duck531a98/esp8266-weather-station-epaper/bitmaps/config.bmp

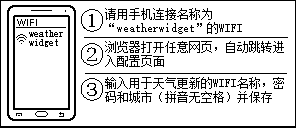
bitmaps/config.bmp
