duck531a98/esp8266-weather-station-epaper/pics/20170623_232157.jpg

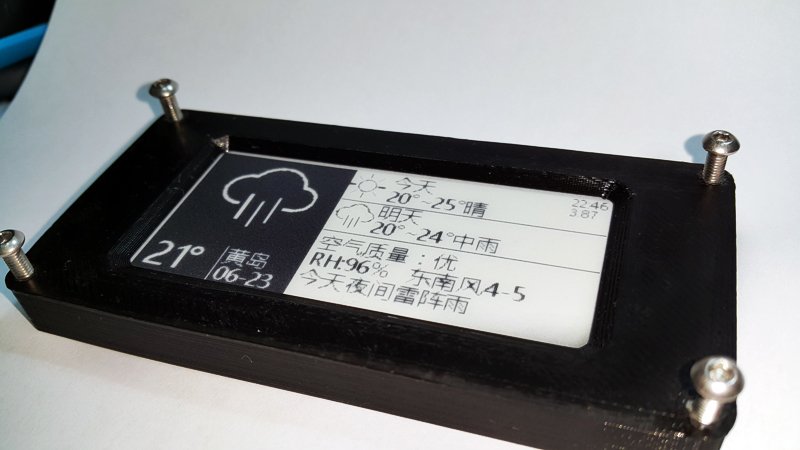
pics/20170623_232157.jpg
