duck531a98/esp8266-weather-station-epaper/pics/20170624_214405.jpg

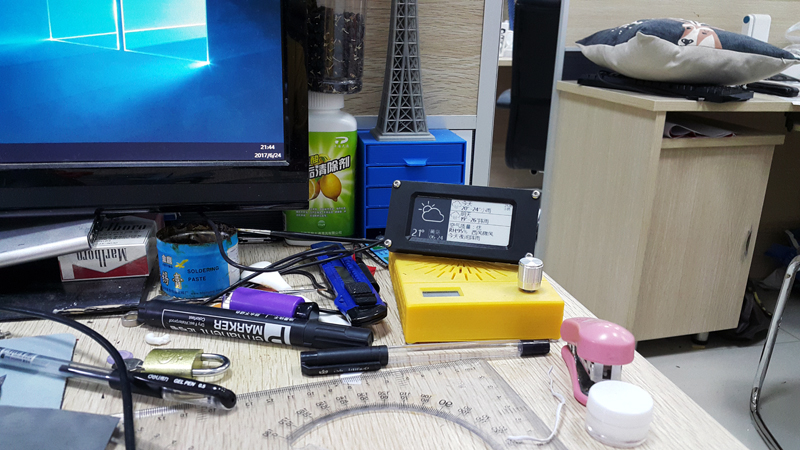
pics/20170624_214405.jpg
