duck531a98/esp8266-weather-station-epaper/pics/20170624_214454.jpg

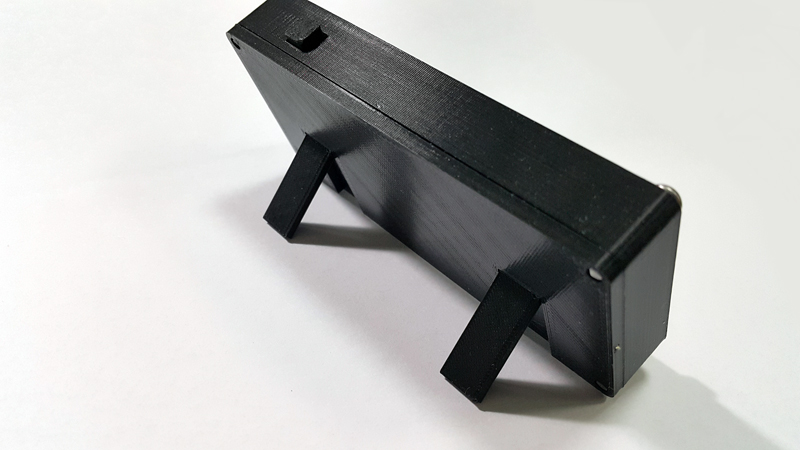
pics/20170624_214454.jpg
