duck531a98/esp8266-weather-station-epaper/pics/20170705_221111.jpg

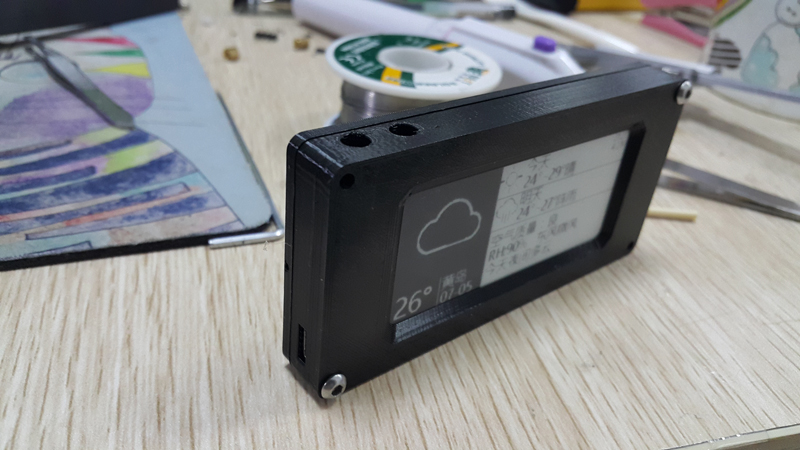
pics/20170705_221111.jpg
