duck531a98/esp8266-weather-station-epaper/pics/20170721_232400.jpg

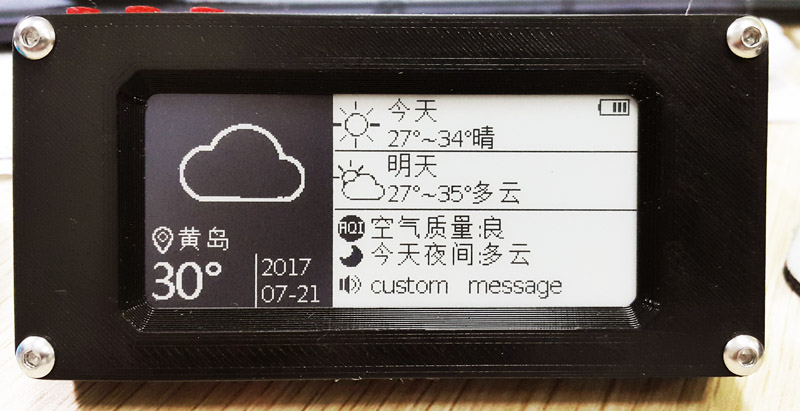
pics/20170721_232400.jpg
