duck531a98/esp8266-weather-station-epaper/pics/20200505_004032.jpg

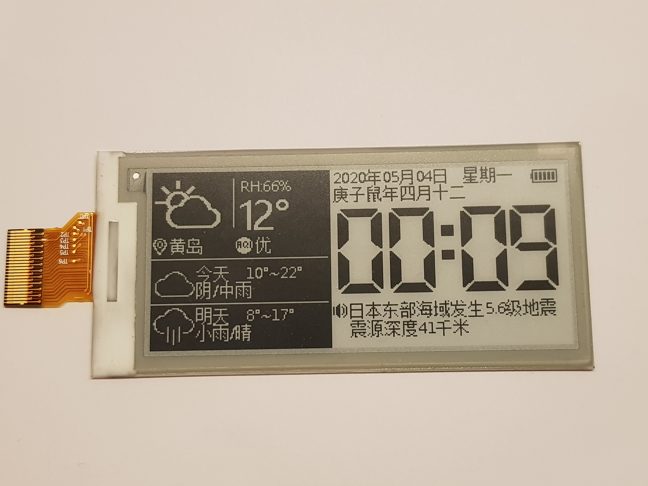
pics/20200505_004032.jpg
