duck531a98/esp8266-weather-station-epaper/EPD_drive.h

#pragma once
 extern unsigned char UNICODEbuffer[200];
 extern const char* fontname;
#ifndef _EPD_DRIVE_H_
#define _EPD_DRIVE_H_
//#include "spline.h"
#include <ESP8266WiFi.h>

  static const unsigned char GDVol[] = {0x03,0x00}; // Gate voltage +15V/-15V
  static  unsigned char GDOControl[]={0x01,39,1,0x00}; //for 1.54inch
  static  unsigned char softstart[]={0x0c,0xd7,0xd6,0x9d};
  static  unsigned char Rambypass[] = {0x21,0x8f};   // Display update
  static unsigned char MAsequency[] = {0x22,0xf0};    // clock 
  static  unsigned char SDVol[] = {0x04,0x0a}; // Source voltage +15V/-15V
  static  unsigned char VCOMVol[] = {0x2c,0xa8}; // VCOM 7c 0xa8
  static unsigned char GateVol[]={0x03,0xea};
  
  static  unsigned char BOOSTERFB[] = {0xf0,0x1f}; // Source voltage +15V/-15V
  static  unsigned char DummyLine[] = {0x3a,0x01}; // 4 dummy line per gate
  static  unsigned char Gatetime[] = {0x3b,B1000};  // 2us per line
  static  unsigned char BorderWavefrom[] = {0x3c,0x63};  // Border
  static  unsigned char RamDataEntryMode[] = {0x11,0x01};  // Ram data entry mode
  static const unsigned char LUTDefault_part[31] = {
    0x32, // command
    0x10,0x18,0x18,0x08,0x18,0x18,0x08,0x00,0x00,0x00,0x00,0x00,0x00,0x00,0x00,0x00,0x00,0x00,0x00,0x00,
    0x13,0x14,0x44,0x12,0x00,0x00,0x00,0x00,0x00,0x00,
    /* 10 wb  01 bw
     * 10 H REPEAT 3
     * 10 H 01 L REPEAT 1
     * 10 H 01 L REPEAT 4
     * 01 L REPEAT 1
     * 10 H 01 L REPEAT 4
     * 10 H 01 L REPEAT 4
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
0x8A ,0x4A ,0x0F ,
0x83 ,0x43 ,0x0C ,
0x06 ,0x4A ,0x04 };
const unsigned char lut_bb_bz03[] ={
  0x24,
0x0E  ,0x14 ,0x01 ,
0x8A ,0x06 ,0x04 ,
0x8A ,0x4A ,0x0F ,
0x83 ,0x43 ,0x0C ,
0x06 ,0x4A ,0x04};
*/
const unsigned char lut_vcomDC_bz03[] ={
0x20,
0x0a ,0x00 ,0x06 ,
0x0a ,0x00 ,0x06 ,
0x0a ,0x00 ,0x06 ,
0x0a ,0x00 ,0x06 ,
0x00 ,0x00 ,0x00 };
const unsigned char lut_ww_bz03[] ={//w
0x21,
0x4a ,0x00 ,0x06,
0x8a ,0x00 ,0x06 ,
0x4A ,0x00 ,0x06 ,
0x8a ,0x00 ,0x06 ,
0x00 ,0x00 ,0x00};
const unsigned char lut_bw_bz03[] ={//b
  0x22,
0x8a  ,0x00 ,0x06 ,
0x4A ,0x00 ,0x06 ,
0x8A ,0x00 ,0x06 ,
0x4a ,0x00 ,0x06 ,
0x00 ,0x00 ,0x00};
const unsigned char lut_wb_bz03[] ={
  0x23,
0x8a  ,0x00 ,0x06 ,
0x4A ,0x00 ,0x06 ,
0x8A ,0x00 ,0x06 ,
0x4a ,0x00 ,0x06 ,
0x00 ,0x00 ,0x00};
const unsigned char lut_bb_bz03[] ={
  0x24,
0x4a ,0x00 ,0x06,
0x8a ,0x00 ,0x06 ,
0x4A ,0x00 ,0x06 ,
0x8a ,0x00 ,0x06 ,
0x00 ,0x00 ,0x00};
const unsigned char lut_vcomDC_part_bz03[] ={
0x20,
0x0a ,0x00 ,0x03 ,
0x00 ,0x00 ,0x00 ,
0x00 ,0x00 ,0x00 ,
0x00 ,0x00 ,0x00 ,
0x00 ,0x00 ,0x00  };
const unsigned char lut_ww_part_bz03[] ={//w
0x21,
0x0a ,0x00 ,0x03,
0x00 ,0x00 ,0x00 ,
0x00 ,0x00 ,0x00 ,
0x00 ,0x00 ,0x00 ,
0x00 ,0x00 ,0x00 };
const unsigned char lut_bb_part_bz03[] ={//01
  0x22,
0x0a ,0x00 ,0x03 ,
0x00 ,0x00 ,0x00 ,
0x00 ,0x00 ,0x00 ,
0x00 ,0x00 ,0x00 ,
0x00 ,0x00 ,0x00 };
const unsigned char lut_bw_part_bz03[] ={//10
  0x23,
0x4a ,0x00 ,0x03 ,
0x00 ,0x00 ,0x00 ,
0x00 ,0x00 ,0x00 ,
0x00 ,0x00 ,0x00 ,
0x00 ,0x00 ,0x00 };
const unsigned char lut_wb_part_bz03[] ={//10
  0x24,
0x8a  ,0x00 ,0x03 ,
0x00 ,0x00 ,0x00 ,
0x00 ,0x00 ,0x00 ,
0x00 ,0x00 ,0x00 ,
0x00 ,0x00 ,0x00};

const unsigned char lut_vcomDC_wf32[] ={
0x20,
0x0a ,0x00 ,0x10 ,
0x0a ,0x00 ,0x10 ,
0x0a ,0x00 ,0x10 ,
0x0a ,0x00 ,0x10 ,
0x00 ,0x00 ,0x00 };
const unsigned char lut_ww_wf32[] ={//ww
0x21,
0x4a ,0x00 ,0x10,
0x8a ,0x00 ,0x10 ,
0x4A ,0x00 ,0x10 ,
0x8A ,0x00 ,0x10 ,
0x00 ,0x00 ,0x00};
const unsigned char lut_bw_wf32[] ={//b
  0x22,
0x8a  ,0x00 ,0x10 ,
0x4A ,0x00 ,0x10 ,
0x8A ,0x00 ,0x10 ,
0x4a ,0x00 ,0x10 ,
0x00 ,0x00 ,0x00};
const unsigned char lut_wb_wf32[] ={//bb
  0x23,
0x8a  ,0x00 ,0x10 ,
0x4A ,0x00 ,0x10 ,
0x8A ,0x00 ,0x10 ,
0x4a ,0x00 ,0x10 ,
0x00 ,0x00 ,0x00};
const unsigned char lut_bb_wf32[] ={//w
  0x24,
0x8a ,0x00 ,0x10,
0x4a ,0x00 ,0x10 ,
0x8A ,0x00 ,0x10 ,
0x8A ,0x00 ,0x10 ,
0x00 ,0x00 ,0x00};
const unsigned char lut_vcomDC_part_wf32[] ={
0x20,
0x0a ,0x00 ,0x04 ,
0x00 ,0x00 ,0x00 ,
0x00 ,0x00 ,0x00 ,
0x00 ,0x00 ,0x00 ,
0x00 ,0x00 ,0x00  };
const unsigned char lut_ww_part_wf32[] ={//w
0x21,
0x0a ,0x00 ,0x04,
0x00 ,0x00 ,0x00 ,
0x00 ,0x00 ,0x00 ,
0x00 ,0x00 ,0x00 ,
0x00 ,0x00 ,0x00 };
const unsigned char lut_bb_part_wf32[] ={//01
0x22,
0x0a ,0x00 ,0x04 ,
0x00 ,0x00 ,0x00 ,
0x00 ,0x00 ,0x00 ,
0x00 ,0x00 ,0x00 ,
0x00 ,0x00 ,0x00 };
const unsigned char lut_bw_part_wf32[] ={//10
0x23,
0x4a ,0x00 ,0x12 ,
0x00 ,0x00 ,0x00 ,
0x00 ,0x00 ,0x00 ,
0x00 ,0x00 ,0x00 ,
0x00 ,0x00 ,0x00 };
const unsigned char lut_wb_part_wf32[] ={//10
0x24,
0x8a  ,0x00 ,0x12 ,
0x00 ,0x00 ,0x00 ,
0x00 ,0x00 ,0x00 ,
0x00 ,0x00 ,0x00 ,
0x00 ,0x00 ,0x00};
enum FONT {
  FONT16 = 0,
  FONT32 = 1,
  FONT10 = 2,
  FONT12 = 3,
  FONT70 =5,
  FONT12_NUM=6,
  FONT24=7,
  FONT8=8,
  DIGI_NUM_100=9,
  ICON_WEATHER=11,
  ICON32=13,
  ICON80=12,
  ICON50=14,
};
enum epd_type{
  WX29=0,
  WF29=1,
  OPM42=2,
  WF58=3,
  WF29BZ03=4,
  C154=5,
  DKE42_3COLOR=6,
  DKE29_3COLOR=7,
  WF42=8,
  WF32=9,
  };
/*
 * 典型使用流程
 * 1.EPD_init_Full/EPD_init_Part初始化
 * 2.clearbuffer清除缓存图像
 * 3.SetFont设置字体
 * 4.fontscale=1设置字体缩放
 * 5.DrawUTF 绘制文字。图像等
 * 6.EPD_DisFull/EPD_Dis_Part更新屏幕图像
 * 7.deepsleep睡眠
 * 
 * 屏幕有圆点的角为（0，0）点，x方向为垂直方向，y方向为水平方向
 */
class Duck_EPD {
public:
  Duck_EPD();
  bool deepsleep(void);
  bool deepsleepAfterTimedRefresh(void);
  
  byte fontscale;///> 字体缩放，仅支持1，2
  byte frame; //用于4灰度屏，fram=0,在2bit中的第一个bit中存储图像，frame=1在第二bit种存储图像
  static const size_t EPD_BUFFER_SIZE = 400UL * 300UL / 8UL;
  // ESP8266 SPI can send aligned buffers directly from the 64-byte FIFO.
  // Keep the frame buffer aligned so full-frame writes need no staging copy.
  alignas(4) unsigned char EPDbuffer[EPD_BUFFER_SIZE];///>屏幕图像；WF58 需分块渲染，不能使用此单缓冲区
  epd_type EPD_Type;
 
  void EPD_Set_Model(byte model);
  void EPD_init_Full(void);
  void EPD_init_Part(void);
  void EPD_Dis_Full(unsigned char *DisBuffer,unsigned char Label);//1正常2全白3全黑
  void EPD_Dis_Part(int xStart,int xEnd,int yStart,int yEnd,unsigned char *DisBuffer,unsigned char Label);
  void EPD_Transfer_Full_BW(unsigned char *DisBuffer,unsigned char Label);
  void EPD_Transfer_Full_RED(unsigned char *DisBuffer,unsigned char Label);
  void EPD_Transfer_Part(int xStart,int xEnd,int yStart,int yEnd,unsigned char *DisBuffer,unsigned char Label);
  
  void SetFont(FONT fontindex);
  void DrawUTF(int16_t x,int16_t y,const String& code);
  void DrawUTF(int16_t x,int16_t y,const char* code);
  void clearbuffer();
  
  void DrawYline(int start,int end, int y);//画竖线
  void DrawXline(int start,int end, int x);//画横线
  void DrawLine(int xstart,int ystart, int xend,int yend);
  void Inverse(int xStart,int xEnd,int yStart,int yEnd);

  void DrawWeatherChart(int xmin,int xmax,int ymin,int ymax,int point_n,int show_n,
                        String tmax,String tmin,String code_d,String code_n,
                        String text_d,String text_n,String date,String week);//绘制天气温度变化曲线
  void DrawCircle(int x,int y,int r,bool fill);//画圆圈，xy圆心，r半径
  void DrawBox(byte x,int y,int w,int h);//画矩形，填充
  void DrawEmptyBox(int x,int y,int w,int h);//画矩形，空心
  void DrawChart(int x,int y,int w, int c1, int c2, int c3, int c4, int c5,int c6);//画水平方向的柱状图，w图表宽度，c1-C6变量
  void DrawCircleChart(int x,int y,int r,int w,int c1,int c2,int c3);//画圆环图表，r半径，w圆环宽，c1-c3变量


  void DrawUnicodeChar(int16_t x,int16_t y,byte width,byte height,unsigned char *code);
  void DrawUnicodeStr(int16_t x,int16_t y,byte width,byte height,byte strlength,unsigned char *code);
  void drawXbm(int16_t xMove, int16_t yMove, int16_t width, int16_t height,unsigned char *xbm);//绘制图像
  void DrawXbm_P(int16_t xMove, int16_t yMove, int16_t width, int16_t height,const unsigned char *xbm);
  void DrawXbm_p_gray(int16_t xMove, int16_t yMove, int16_t width, int16_t height,const unsigned char *xbm,byte level);
  void DrawXbm_spiff_gray(int16_t xMove, int16_t yMove, int16_t width, int16_t height,byte level);

  void EPD_Write(unsigned char *value, unsigned char datalen);
  void EPD_WriteCMD(unsigned char command);
  void EPD_WriteData (unsigned char data);
  void EPD_WriteCMD_p1(unsigned char command,unsigned char para); 
  unsigned char ReadBusy(void);
  unsigned char ReadBusy_long(void);
  bool hasBusyTimedOut(void) const {return busyTimedOut;}
  void EPD_Set_Contrast(byte vcom);

  void EPD_Update(void);
  void EPD_Update_Part(void);
  void EPD_WriteDispRam_Old(unsigned int XSize,unsigned int YSize,unsigned char *Dispbuff,unsigned int offset,byte label);
private:
  byte FontIndex; 
  
  int xDot;
 int yDot;
  int16_t CurrentCursor;
  byte fontwidth;
  byte fontheight;
  bool busyTimedOut=false;
	
	
	
  unsigned char WaitBusy(unsigned long timeoutMs,bool ignorePreviousTimeout);
  bool deepsleepImpl(bool refreshAlreadySettled);
  void EPD_WriteDispRam_RED(unsigned int XSize,unsigned int YSize,unsigned char *Dispbuff,unsigned int offset,byte label);
  void EPD_WriteDispRam(unsigned int XSize,unsigned int YSize,unsigned char *Dispbuff,unsigned int offset,byte label);	
	void EPD_SetRamArea(uint16_t Xstart,uint16_t Xend,unsigned char Ystart,unsigned char Ystart1,unsigned char Yend,unsigned char Yend1);
	void EPD_SetRamPointer(uint16_t addrX,unsigned char addrY,unsigned char addrY1);
	void EPD_WirteLUT(unsigned char *LUTvalue,unsigned char Size);

  
	void EPD_Init(void);
  
  

  int getIcon(int weathercodeindex);
  void SetPixel(int16_t x, int16_t y);
  void InversePixel(int16_t x, int16_t y);
  void DrawUTF(int16_t x,int16_t y,byte width,byte height,unsigned char *code);
  int UTFtoUNICODE(unsigned char *code);



};

#endif
