duck531a98/esp8266-weather-station-epaper/bitmaps.h

//体感温度
const unsigned char PROGMEM fl[24] = {/* 0X01,0X01,0X0C,0X00,0X0C,0X00, */
0X00,0X00,0X00,0X00,0X00,0X00,0X00,0XC0,0XFF,0X20,0X80,0X10,0XAA,0X10,0XFF,0X20,
0X00,0XC0,0X00,0X00,0X00,0X00,0X00,0X00,};
//风向
const unsigned char PROGMEM dir[24] = { /* 0X01,0X01,0X0C,0X00,0X0C,0X00, */
0X0F,0X00,0X30,0XC0,0X40,0X20,0X4C,0X20,0X9C,0X10,0XBF,0XD0,0XBF,0XD0,0X9C,0X10,
0X4C,0X20,0X40,0X20,0X30,0XC0,0X0F,0X00,};
//风力
const unsigned char PROGMEM sc[24] = {/* 0X01,0X01,0X0C,0X00,0X0C,0X00, */
0X00,0X00,0X00,0X00,0X00,0X00,0XFF,0XF0,0XFE,0X00,0X7C,0X00,0X7C,0X00,0X38,0X00,
0X10,0X00,0X00,0X00,0X00,0X00,0X00,0X00,};
//降水量
const unsigned char PROGMEM pcpn[24] = {/* 0X01,0X01,0X0C,0X00,0X0C,0X00, */
0X03,0X00,0X0F,0XC0,0X38,0X60,0X60,0X20,0XC0,0X30,0X80,0X10,0X8C,0XD0,0X47,0XB0,
0X60,0X20,0X38,0X60,0X0F,0XC0,0X03,0X00,};
//能见度
const unsigned char PROGMEM vis[24] = {/* 0X01,0X01,0X0C,0X00,0X0C,0X00, */
0X04,0X00,0X1B,0X00,0X11,0X00,0X20,0X80,0X2E,0X80,0X2A,0X80,0X2A,0X80,0X2E,0X80,
0X20,0X80,0X11,0X00,0X1B,0X00,0X04,0X00,};
//气压
const unsigned char PROGMEM pres[24] = { /* 0X01,0X01,0X0C,0X00,0X0C,0X00, */
0X06,0X00,0X0E,0X00,0X1C,0X00,0X38,0X00,0X30,0X00,0X70,0XC0,0X71,0XC0,0X72,0X00,
0X34,0X00,0X38,0X00,0X1C,0X00,0X2E,0X00,};


const unsigned char PROGMEM message[24] ={ /* 0X01,0X01,0X0C,0X00,0X0C,0X00, */
0X00,0X00,0X1F,0X80,0X00,0X00,0X1F,0X80,0X3F,0XC0,0X7F,0XE0,0X00,0X00,0X10,0X80,
0X4F,0X20,0X20,0X40,0X1F,0X80,0X00,0X00,};

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
0X86,0X67,0X65,0X43,0X34,0X44,0X44,0X33,0X33,0X33,0X44,0X44,0X56,0X66,0X87,0X55,
0X98,0X88,0X9B,0XC8,0XBD,0XA6,0XA8,0XB8,0X6A,0XBA,0XEB,0X99,0XA9,0XAA,0XDE,0XBC,
0XED,0XDC,0XCD,0XDB,0XBB,0XCC,0XBA,0XAC,0XCA,0X98,0X99,0X87,0XCC,0XCC,0XCC,0XCC,
0XCC,0XDD,0XDD,0XDD,0XDD,0XEE,0XEE,0XED,0XDD,0XDB,0XDD,0XCA,0XCC,0XCD,0XDD,0XDD,
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
