duck531a98/esp8266-weather-station-epaper/gray_image.h

const unsigned char PROGMEM wf32[] =   { /* 0X01,0X04,0XA5,0X00,0X5A,0X00, */
0X00,0X00,0X00,0X00,0X00,0X00,0X00,0X00,0X00,0X00,0X00,0X00,0X00,0X00,0X00,0X00,
0X00,0X00,0X00,0X00,0X00,0X00,0X00,0X00,0X00,0X00,0X00,0X00,0X00,0X00,0X00,0X00,
0X00,0X00,0X00,0X00,0X00,0X00,0X00,0X01,0X07,0XEE,0XDE,0XCD,0XDC,0X00,0X00,0X00,
0X00,0X00,0X00,0X00,0X00,0X00,0X00,0X00,0X00,0X00,0X00,0X00,0X00,0X00,0X00,0X00,
0X00,0X00,0X00,0X00,0X00,0X00,0X00,0X00,0X00,0X00,0X00,0X00,0X00,0X00,0X00,0X00,
0X00,0X00,0X00,0X00,0X00,0X19,0XDD,0XDE,0XDD,0XDD,0X00,0X00,0X00,0X00,0X00,0X00,
0X00,0X00,0X00,0X00,0X00,0X00,0X00,0X00,0X00,0X00,0X23,0X67,0X67,0X99,0X76,0X31,
0X00,0X10,0X00,0X00,0X00,0X00,0X00,0X00,0X00,0X00,0X00,0X00,0X00,0X00,0X00,0X00,
0X00,0X00,0X1C,0XDC,0XDD,0XED,0XDD,0X00,0X00,0X00,0X00,0X00,0X00,0X00,0X00,0X00,
0X00,0X00,0X11,0X13,0X34,0X55,0X66,0X75,0X69,0XAB,0XCB,0X9A,0XB9,0X40,0X00,0X00,
0X00,0X00,0X00,0X00,0X00,0X00,0X00,0X00,0X00,0X00,0X00,0X00,0X00,0X00,0X00,0X0B,
0XCC,0XCC,0XDC,0XCD,0X00,0X00,0X00,0X00,0X00,0X00,0X00,0X00,0X00,0X00,0X01,0X33,
0X47,0X76,0X55,0X87,0X54,0X47,0X9A,0XBB,0XCA,0X76,0X77,0X75,0X53,0X21,0X11,0X00,
0X00,0X00,0X00,0X00,0X00,0X00,0X00,0X00,0X00,0X00,0X00,0X00,0X29,0XAB,0XBB,0XBC,
0XCC,0X00,0X00,0X00,0X00,0X00,0X00,0X00,0X00,0X00,0X01,0X24,0X66,0X67,0X66,0X56,
0X87,0X55,0X56,0X79,0XBB,0XA8,0X45,0X9A,0XA8,0X87,0X67,0X75,0X31,0X00,0X00,0X00,
0X01,0X11,0X11,0X10,0X00,0X00,0X00,0X00,0X01,0X8B,0XBC,0XCC,0XBC,0XCC,0X00,0X00,
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
0X00,0X00,0X00,0X00,0X00,0X00,0X00,0X00,0X00,0X00,0X00,0X00,0X00,0X00,0X00,0X00,
0X00,0X00,0X00,0X00,0X00,0X00,0X00,0X00,0X00,0X00,0X00,0X00,0X00,0X00,0X00,0X00,
0X00,0X00,0X00,0X00,0X00,0X00,0X00,0X00,0X00,0X00,0X00,0X00,0X00,0X00,0X00,0X00,
0X00,};
